MOSH-Insa-Toulouse/LEON-Florian_KHALED-Walid_GENEAU-Teo_MOSH-Project/LTSPICE/Résultats_simulation/Partie_1/Circuit_complet.PNG

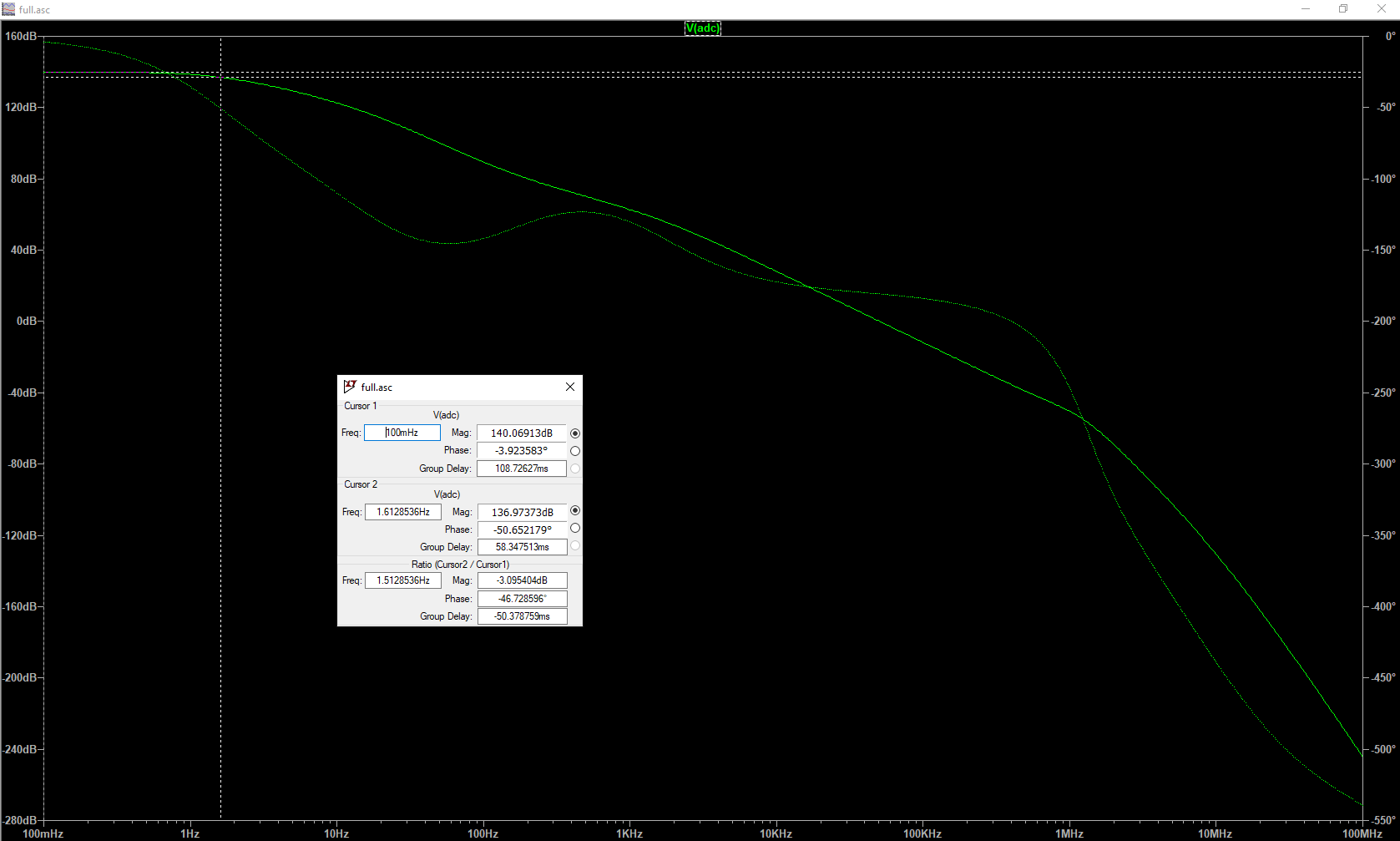
LTSPICE/Résultats_simulation/Partie_1/Circuit_complet.PNG
