MOSH-Insa-Toulouse/LEON-Florian_KHALED-Walid_GENEAU-Teo_MOSH-Project/LTSPICE/Résultats_simulation/Partie_1/Etage_2_filtre_milieu.PNG

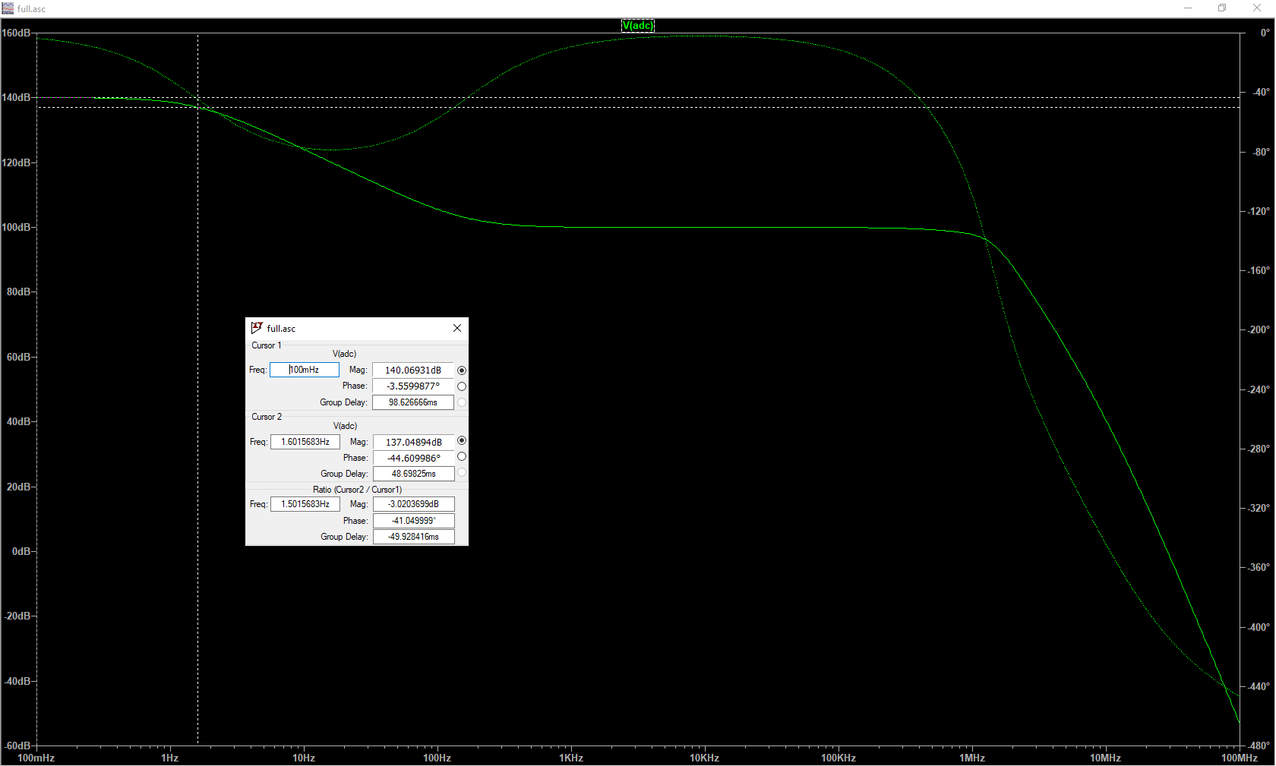
LTSPICE/Résultats_simulation/Partie_1/Etage_2_filtre_milieu.PNG
