MOSH-Insa-Toulouse/LEON-Florian_KHALED-Walid_GENEAU-Teo_MOSH-Project/LTSPICE/Résultats_simulation/Partie_1/Etage_3_filtre_droit.PNG

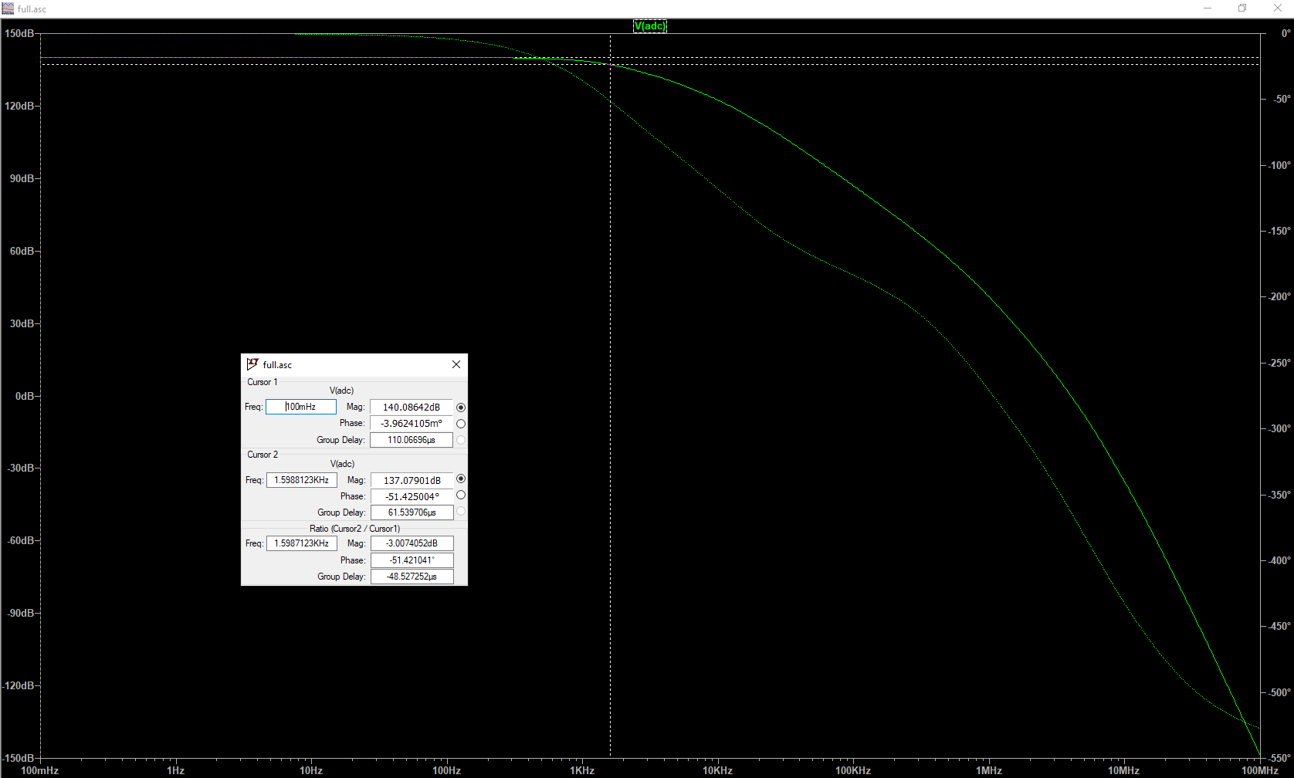
LTSPICE/Résultats_simulation/Partie_1/Etage_3_filtre_droit.PNG
