MOSH-Insa-Toulouse/LEON-Florian_KHALED-Walid_GENEAU-Teo_MOSH-Project/LTSPICE/Simulation_circuit_interrupt/Simulation interruption physique mosh3.PNG

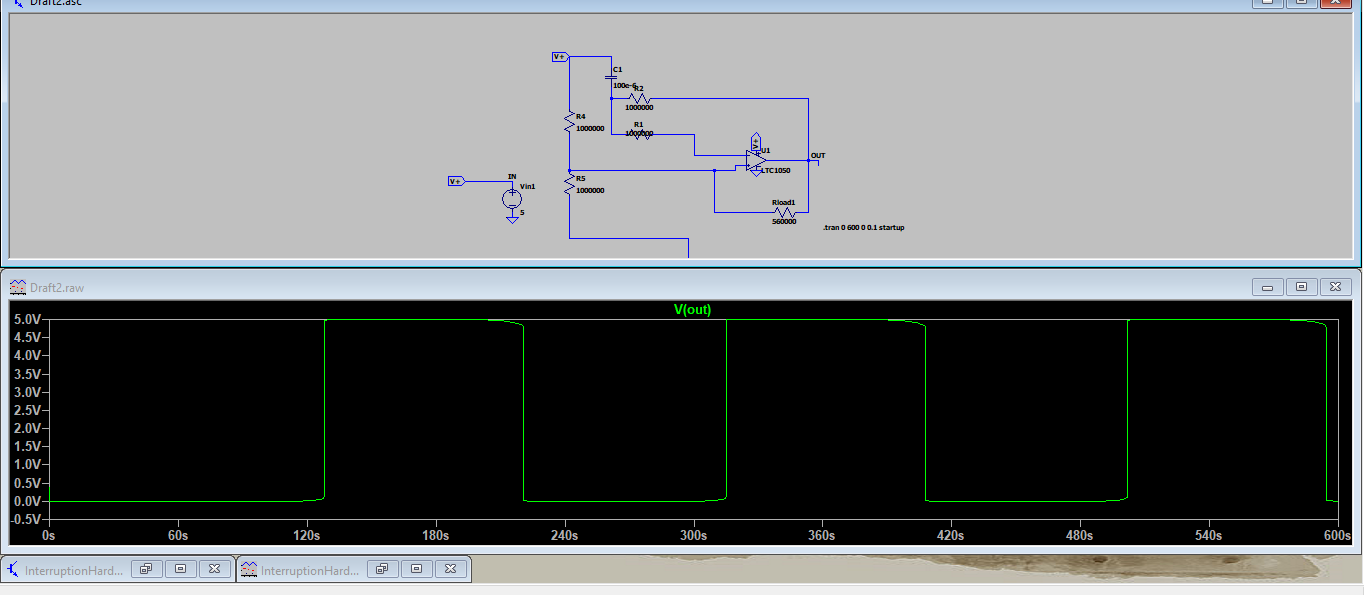
LTSPICE/Simulation_circuit_interrupt/Simulation interruption physique mosh3.PNG
