MOSH-Insa-Toulouse/LEON-Florian_KHALED-Walid_GENEAU-Teo_MOSH-Project/Photos/sleep.jpg

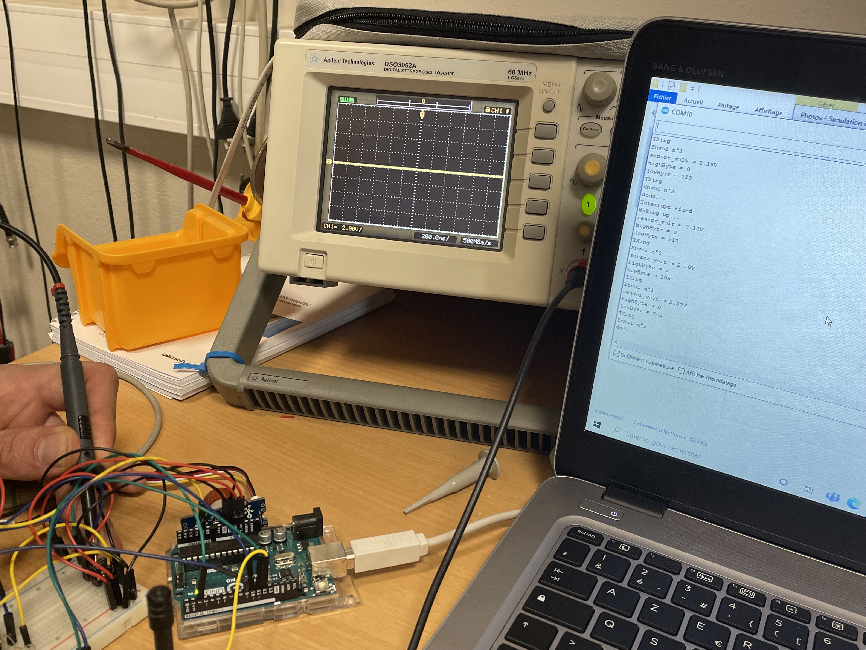
Photos/sleep.jpg
