MOSH-Insa-Toulouse/LEON-Florian_KHALED-Walid_GENEAU-Teo_MOSH-Project/LTSPICE/TP_elec/essai.asc

C1: cap; 100p
R1: res; 10k
V1: voltage; PULSE(0 1 10u 1u 1u 10u); AC 1.
Named nets: 0, my-out
;tran 30u
.ac dec 100 1 0.1G
