MOSH-Insa-Toulouse/LEON-Florian_KHALED-Walid_GENEAU-Teo_MOSH-Project/LTSPICE/TP_elec/full_remplacement.asc

C1: cap; 100n
C2: cap; 1µ
C3: cap; 100n
C4: cap; 100n
C5: cap; 1p
R1: res; 10k
R2: res; 100k
R3: res; 1k
R4: res; 100k
R5: res; 1k
U1: LTC1050
V1: voltage; 5
V2: voltage; SINE(0 325 50); AC 1.
V3: voltage; PULSE(0 1 0.2 0.1 0.1 20)
X1: SymbCapteurGaz
Named nets: 0, ADC, Isens
.tran 30
;ac dec 100 0.1 0.1G
