MOSH-Insa-Toulouse/LEON-Florian_KHALED-Walid_GENEAU-Teo_MOSH-Project/LTSPICE/TP_elec/partie2.asc

V1: voltage
V2: voltage
V3: voltage
X1: SymbCapteurGaz
