MOSH-Insa-Toulouse/LEON-Florian_KHALED-Walid_GENEAU-Teo_MOSH-Project/LTSPICE/TP_elec/SymbCapteurGaz.asc

B1: bi; I=V(cp,cn)*(10n+v(gc,gn)*10n)
C1: cap; 200p
R1: res; 1k
Named nets: gc, gp, gn, cp, cn
